vuoz/chalk/imgs/IMG_5259.jpeg

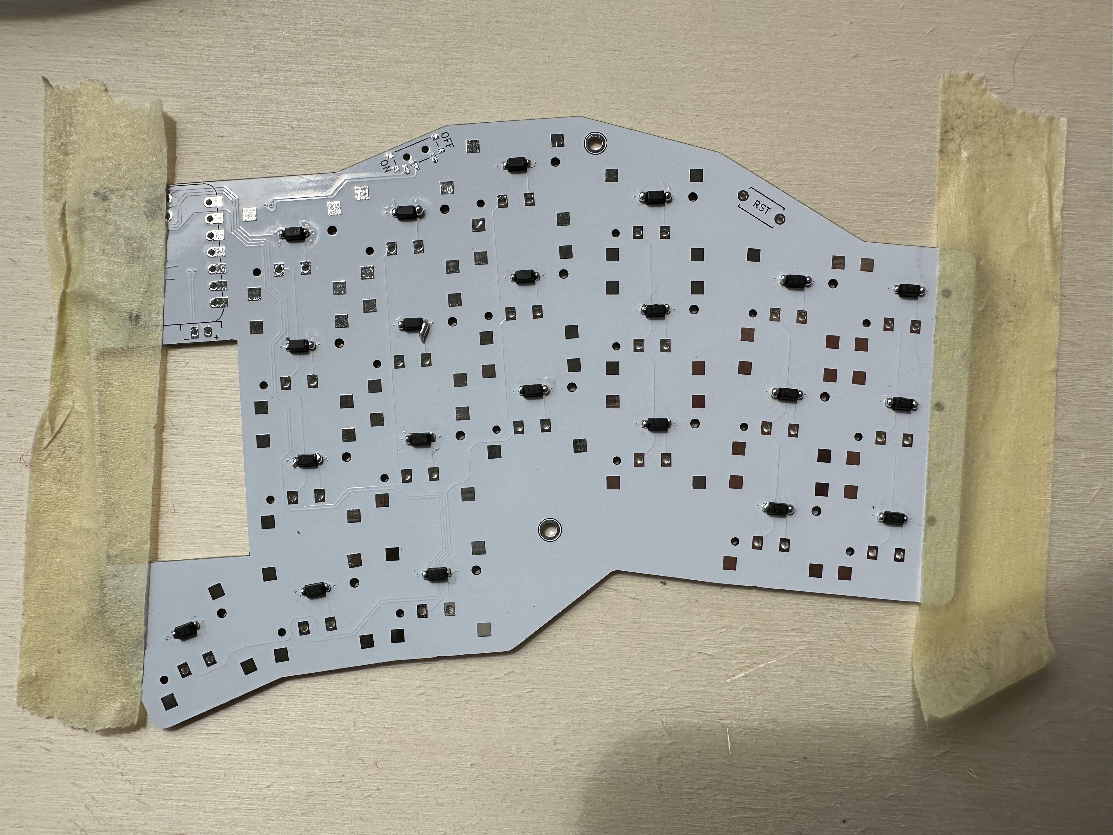
imgs/IMG_5259.jpeg
