vuoz/chalk/imgs/IMG_5261.jpeg

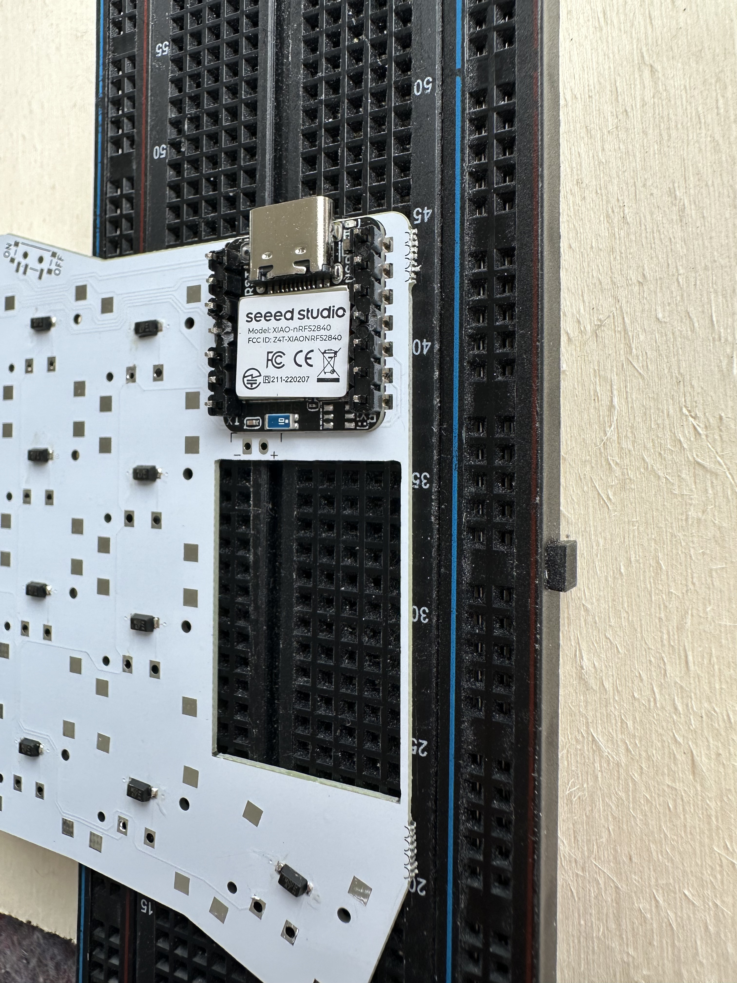
imgs/IMG_5261.jpeg
