vuoz/chalk/imgs/IMG_5272.jpeg

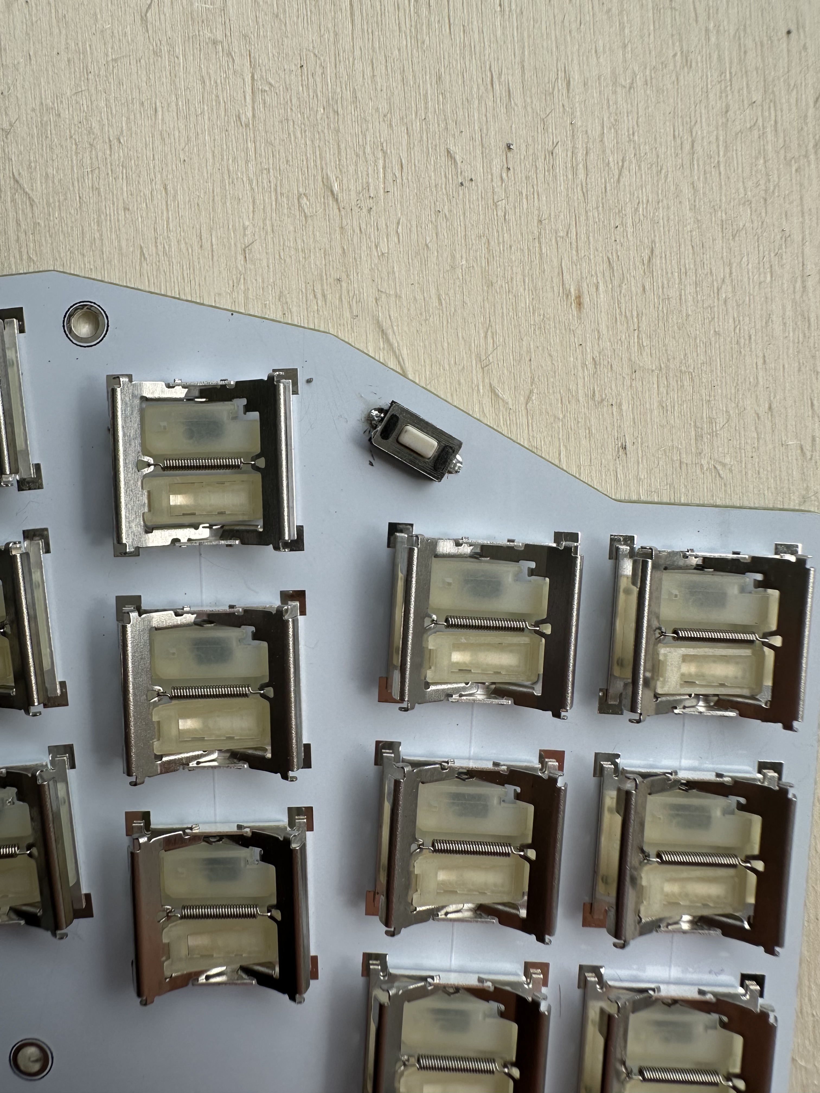
imgs/IMG_5272.jpeg
