vuoz/chalk/imgs/IMG_5293.jpeg

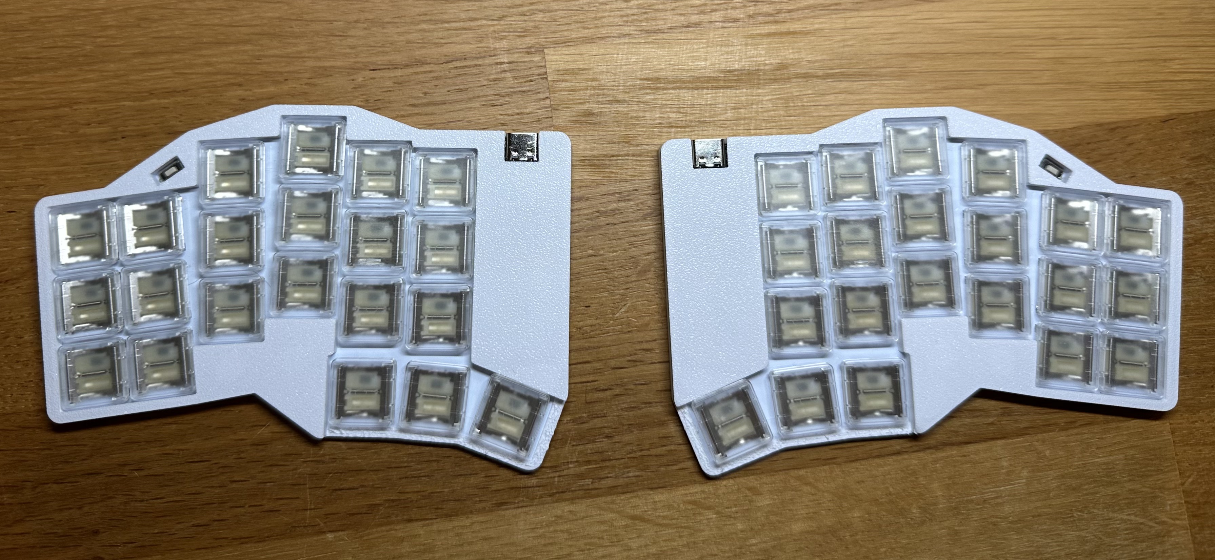
imgs/IMG_5293.jpeg
