vuoz/chalk/imgs/IMG_5308.jpeg

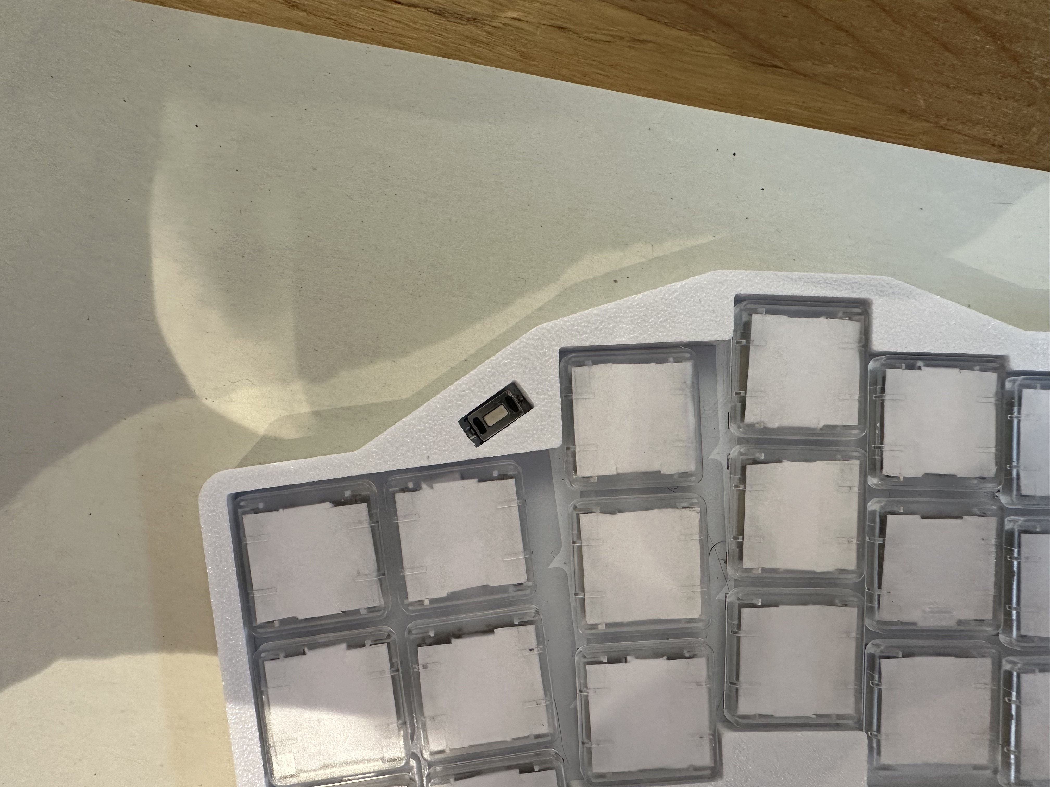
imgs/IMG_5308.jpeg
