vuoz/chalk/imgs/IMG_5312.jpeg

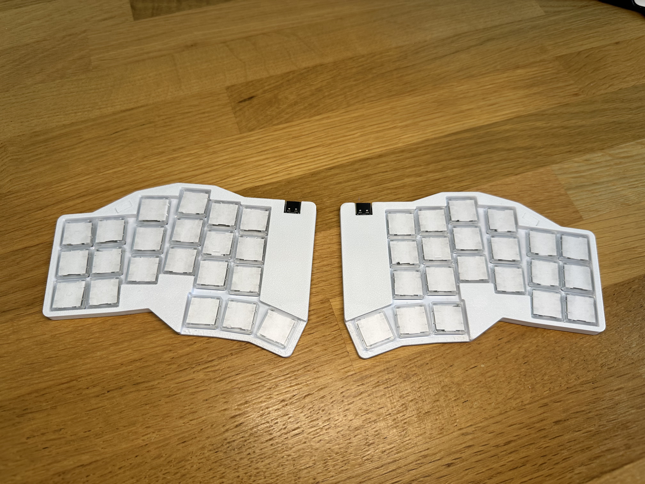
imgs/IMG_5312.jpeg
