vuoz/chalk/imgs/IMG_5434.jpeg

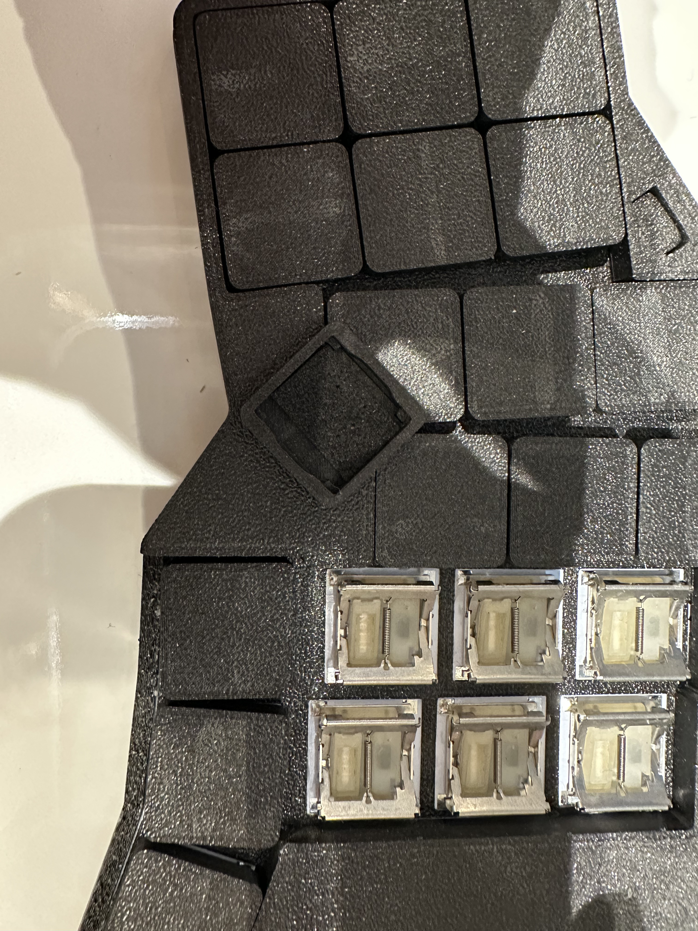
imgs/IMG_5434.jpeg
